sparkfunX/DGNSS-Ranger/Firmware/LidarRanger_withconfig_proto/secrets.h

//WiFi credentials
const char ssid[] = "乇乂丁尺卂丁卄丨匚匚";
const char password[] =  "egub047(";

//RTK2Go
const char casterHost[] = "rtk2go.com"; 
const uint16_t casterPort = 2101;
const char casterUser[] = "nick.poole@sparkfun.com";
const char casterUserPW[] = "";
const char mountPoint[] = "GreatBigFactory_VA"; 
